tomoya723/FULLMONI-Legacy/FullMoni/FullMoni/iodefine.h

// --------------------------------------------------------------------
// Copylight (C) 2021, Tomoya Sato( https://blog.goo.ne.jp/nacci_tomoya )
//
// This file is part of FullMoni firmwere.
//
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
// filename		:	iodefine.h
// brief		:	FullMoni rev.C IO DEFINE
// author		:	Tomoya Sato
// update		:	2021/02/21
// version		:	1.06
// --------------------------------------------------------------------

// --------------------------------------------------------------------
// 多重インクルード防止
// --------------------------------------------------------------------
#ifndef _IODEFINE_H_
#define _IODEFINE_H_

/************************************************************************/
/*      H8SX/1655 Group Include File                       Version 1.0  */
/************************************************************************/
struct st_usb {                                         /* struct USBF  */
              union {                                   /* IFR0         */
                    unsigned char BYTE;                 /*  Byte Access */
                    struct {                            /*  Bit  Access */
                           unsigned char BRST    :1;    /*    BRST      */
                           unsigned char EP1FULL :1;    /*    EP1FULL   */
                           unsigned char EP2TR   :1;    /*    EP2TR     */
                           unsigned char EP2EMPTY:1;    /*    EP2EMPTY  */
                           unsigned char SETUPTS :1;    /*    SETUPTS   */
                           unsigned char EP0oTS  :1;    /*    EP0oTS    */
                           unsigned char EP0iTR  :1;    /*    EP0iTR    */
                           unsigned char EP0iTS  :1;    /*    EP0iTS    */
                           }      BIT;                  /*              */
                    }           IFR0;                   /*              */
              union {                                   /* IFR1         */
                    unsigned char BYTE;                 /*  Byte Access */
                    struct {                            /*  Bit  Access */
                           unsigned char       :4;      /*              */
                           unsigned char VBUSMN:1;      /*    VBUSMN    */
                           unsigned char EP3TR :1;      /*    EP3TR     */
                           unsigned char EP3TS :1;      /*    EP3TS     */
                           unsigned char VBUSF :1;      /*    VBUSF     */
                           }      BIT;                  /*              */
                    }           IFR1;                   /*              */
              union {                                   /* IFR2         */
                    unsigned char BYTE;                 /*  Byte Access */
                    struct {                            /*  Bit  Access */
                           unsigned char      :2;       /*              */
                           unsigned char SURSS:1;       /*    SURSS     */
                           unsigned char SURSF:1;       /*    SURSF     */
                           unsigned char CFDN :1;       /*    CFDN      */
                           unsigned char      :1;       /*              */
                           unsigned char SETC :1;       /*    SETC      */
                           unsigned char SETI :1;       /*    SETI      */
                           }      BIT;                  /*              */
                    }           IFR2;                   /*              */
              char              wk1;                    /*              */
              union {                                   /* IER0         */
                    unsigned char BYTE;                 /*  Byte Access */
                    struct {                            /*  Bit  Access */
                           unsigned char BRST    :1;    /*    BRST      */
                           unsigned char EP1FULL :1;    /*    EP1FULL   */
                           unsigned char EP2TR   :1;    /*    EP2TR     */
                           unsigned char EP2EMPTY:1;    /*    EP2EMPTY  */
                           unsigned char SETUPTS :1;    /*    SETUPTS   */
                           unsigned char EP0oTS  :1;    /*    EP0oTS    */
                           unsigned char EP0iTR  :1;    /*    EP0iTR    */
                           unsigned char EP0iTS  :1;    /*    EP0iTS    */
                           }      BIT;                  /*              */
                    }           IER0;                   /*              */
              union {                                   /* IER1         */
                    unsigned char BYTE;                 /*  Byte Access */
                    struct {                            /*  Bit  Access */
                           unsigned char       :5;      /*              */
                           unsigned char EP3TR :1;      /*    EP3TR     */
                           unsigned char EP3TS :1;      /*    EP3TS     */
                           unsigned char VBUSF :1;      /*    VBUSF     */
                           }      BIT;                  /*              */
                    }           IER1;                   /*              */
              union {                                   /* IER2         */
                    unsigned char BYTE;                 /*  Byte Access */
                    struct {                            /*  Bit  Access */
                           unsigned char SSRSME:1;      /*    SSRSME    */
                           unsigned char       :2;      /*              */
                           unsigned char SURSE :1;      /*    SURSE     */
                           unsigned char CFDN  :1;      /*    CFDN      */
                           unsigned char       :1;      /*              */
                           unsigned char SETCE :1;      /*    SETCE     */
                           unsigned char SETIE :1;      /*    SETIE     */
                           }      BIT;                  /*              */
                    }           IER2;                   /*              */
              char              wk2;                    /*              */
              union {                                   /* ISR0         */
                    unsigned char BYTE;                 /*  Byte Access */
                    struct {                            /*  Bit  Access */
                           unsigned char BRST    :1;    /*    BRST      */
                           unsigned char EP1FULL :1;    /*    EP1FULL   */
                           unsigned char EP2TR   :1;    /*    EP2TR     */
                           unsigned char EP2EMPTY:1;    /*    EP2EMPTY  */
                           unsigned char SETUPTS :1;    /*    SETUPTS   */
                           unsigned char EP0oTS  :1;    /*    EP0oTS    */
                           unsigned char EP0iTR  :1;    /*    EP0iTR    */
                           unsigned char EP0iTS  :1;    /*    EP0iTS    */
                           }      BIT;                  /*              */
                    }           ISR0;                   /*              */
              union {                                   /* ISR1         */
                    unsigned char BYTE;                 /*  Byte Access */
                    struct {                            /*  Bit  Access */
                           unsigned char       :5;      /*              */
                           unsigned char EP3TR :1;      /*    EP3TR     */
                           unsigned char EP3TS :1;      /*    EP3TS     */
                           unsigned char VBUSF :1;      /*    VBUSF     */
                           }      BIT;                  /*              */
                    }           ISR1;                   /*              */
              union {                                   /* ISR2         */
                    unsigned char BYTE;                 /*  Byte Access */
                    struct {                            /*  Bit  Access */
                           unsigned char      :3;       /*              */
                           unsigned char SURSE:1;       /*    SURSE     */
                           unsigned char CFDN :1;       /*    CFDN      */
                           unsigned char      :1;       /*              */
                           unsigned char SETCE:1;       /*    SETCE     */
                           unsigned char SETIE:1;       /*    SETIE     */
                           }      BIT;                  /*              */
                    }           ISR2;                   /*              */
              char              wk3;                    /*              */
              unsigned char     EPDR0i;                 /* EPDR0i       */
              unsigned char     EPDR0o;                 /* EPDR0o       */
              unsigned char     EPDR0s;                 /* EPDR0s       */
              char              wk4;                    /*              */
              unsigned char     EPDR1;                  /* EPDR1        */
              char              wk5[3];                 /*              */
              unsigned char     EPDR2;                  /* EPDR2        */
              char              wk6[3];                 /*              */
              unsigned char     EPDR3;                  /* EPDR3        */
              char              wk7[11];                /*              */
              unsigned char     EPSZ0o;                 /* EPSZ0o       */
              unsigned char     EPSZ1;                  /* EPSZ1        */
              char              wk8;                    /*              */
              union {                                   /* DASTS        */
                    unsigned char BYTE;                 /*  Byte Access */
                    struct {                            /*  Bit  Access */
                           unsigned char       :2;      /*              */
                           unsigned char EP3DE :1;      /*    EP3DE     */
                           unsigned char EP2DE :1;      /*    EP2DE     */
                           unsigned char       :3;      /*              */
                           unsigned char EP0iDE:1;      /*    EP0iDE    */
                           }      BIT;                  /*              */
                    }           DASTS;                  /*              */
              union {                                   /* FCLR         */
                    unsigned char BYTE;                 /*  Byte Access */
                    struct {                            /*  Bit  Access */
                           unsigned char        :1;     /*              */
                           unsigned char EP3CLR :1;     /*    EP3CLR    */
                           unsigned char EP1CLR :1;     /*    EP1CLR    */
                           unsigned char EP2CLR :1;     /*    EP2CLR    */
                           unsigned char        :2;     /*              */
                           unsigned char EP0oCLR:1;     /*    EP0oCLR   */
                           unsigned char EP0iCLR:1;     /*    EP0iCLR   */
                           }      BIT;                  /*              */
                    }           FCLR;                   /*              */
              char              wk9;                    /*              */
              union {                                   /* EPSTL        */
                    unsigned char BYTE;                 /*  Byte Access */
                    struct {                            /*  Bit  Access */
                           unsigned char       :4;      /*              */
                           unsigned char EP3STL:1;      /*    EP3STL    */
                           unsigned char EP2STL:1;      /*    EP2STL    */
                           unsigned char EP1STL:1;      /*    EP1STL    */
                           unsigned char EP0STL:1;      /*    EP0STL    */
                           }      BIT;                  /*              */
                    }           EPSTL;                  /*              */
              char              wk10;                   /*              */
              union {                                   /* TRG          */
                    unsigned char BYTE;                 /*  Byte Access */
                    struct {                            /*  Bit  Access */
                           unsigned char         :1;    /*              */
                           unsigned char EP3PKTE :1;    /*    EP3PKTE   */
                           unsigned char EP1RDFN :1;    /*    EP1RDFN   */
                           unsigned char EP2PKTE :1;    /*    EP2PKTE   */
                           unsigned char         :1;    /*              */
                           unsigned char EP0sRDFN:1;    /*    EP0sRDFN  */
                           unsigned char EP0oRDFN:1;    /*    EP0oRDFN  */
                           unsigned char EP0iPKTE:1;    /*    EP0iPKTE  */
                           }      BIT;                  /*              */
                    }           TRG;                    /*              */
              union {                                   /* DMA          */
                    unsigned char BYTE;                 /*  Byte Access */
                    struct {                            /*  Bit  Access */
                           unsigned char         :5;    /*              */
                           unsigned char PULLUPE :1;    /*    PULLUP_E  */
                           unsigned char EP2DMAE :1;    /*    EP2DMAE   */
                           unsigned char EP1DMAE :1;    /*    EP1DMAE   */
                           }      BIT;                  /*              */
                    }           DMA;                    /*              */
              union {                                   /* CVR          */
                    unsigned char BYTE;                 /*  Byte Access */
                    struct {                            /*  Bit  Access */
                           unsigned char CNFV:2;        /*    CNFV      */
                           unsigned char INTV:2;        /*    INTV      */
                           unsigned char     :1;        /*              */
                           unsigned char ALTV:3;        /*    ALTV      */
                           }      BIT;                  /*              */
                    }           CVR;                    /*              */
              union {                                   /* CTLR         */
                    unsigned char BYTE;                 /*  Byte Access */
                    struct {                            /*  Bit  Access */
                           unsigned char      :3;       /*              */
                           unsigned char RWUPS:1;       /*    RWUPS     */
                           unsigned char RSME :1;       /*    RSME      */
                           unsigned char PWMD :1;       /*    PWMD      */
                           unsigned char ASCE :1;       /*    ASCE      */
                           }      BIT;                  /*              */
                    }           CTLR;                   /*              */
              char              wk11[2];                /*              */
              unsigned char     EPIR;                   /* EPIR         */
              char              wk12[17];               /*              */
              union {                                   /* TRNTREG0     */
                    unsigned char BYTE;                 /*  Byte Access */
                    struct {                            /*  Bit  Access */
                           unsigned char PTSTE  :1;     /*    PTSTE     */
                           unsigned char        :3;     /*              */
                           unsigned char SUSPEND:1;     /*    SUSPEND   */
                           unsigned char txenl  :1;     /*    txenl     */
                           unsigned char Txse0  :1;     /*    Txse0     */
                           unsigned char Txdata :1;     /*    Txdata    */
                           }      BIT;                  /*              */
                    }           TRNTREG0;               /*              */
              union {                                   /* TRNTREG1     */
                    unsigned char BYTE;                 /*  Byte Access */
                    struct {                            /*  Bit  Access */
                           unsigned char          :5;   /*              */
                           unsigned char xverdata :1;   /*    xver_data */
                           unsigned char dpls     :1;   /*    dpls      */
                           unsigned char dmns     :1;   /*    dmns      */
                           }      BIT;                  /*              */
                     }          TRNTREG1;               /*              */
};                                                      /*              */
struct st_p1 {                                          /* struct P1    */
             unsigned char      DDR;                    /* P1DDR        */
             char               wk1[15];                /*              */
             union {                                    /* P1ICR        */
                   unsigned char BYTE;                  /*  Byte Access */
                   struct {                             /*  Bit  Access */
                          unsigned char B7:1;           /*    Bit 7     */
                          unsigned char B6:1;           /*    Bit 6     */
                          unsigned char B5:1;           /*    Bit 5     */
                          unsigned char B4:1;           /*    Bit 4     */
                          unsigned char B3:1;           /*    Bit 3     */
                          unsigned char B2:1;           /*    Bit 2     */
                          unsigned char B1:1;           /*    Bit 1     */
                          unsigned char B0:1;           /*    Bit 0     */
                          }      BIT;                   /*              */
                   }            ICR;                    /*              */
             char               wk2[943];               /*              */
             union {                                    /* P1PORT       */
                   unsigned char BYTE;                  /*  Byte Access */
                   struct {                             /*  Bit  Access */
                          unsigned char B7:1;           /*    Bit 7     */
                          unsigned char B6:1;           /*    Bit 6     */
                          unsigned char B5:1;           /*    Bit 5     */
                          unsigned char B4:1;           /*    Bit 4     */
                          unsigned char B3:1;           /*    Bit 3     */
                          unsigned char B2:1;           /*    Bit 2     */
                          unsigned char B1:1;           /*    Bit 1     */
                          unsigned char B0:1;           /*    Bit 0     */
                          }      BIT;                   /*              */
                   }            PORT;                   /*              */
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
                    struct {                            /*  Bit  Access */
                           unsigned char CS7S:2;        /*    CS7S      */
                           unsigned char CS6S:2;        /*    CS6S      */
                           unsigned char CS5S:2;        /*    CS5S      */
                           }      BIT;                  /*              */
                    }           PFCR1;                  /*              */
              union {                                   /* PFCR2        */
                    unsigned char BYTE;                 /*  Byte Access */
                    struct {                            /*  Bit  Access */
                           unsigned char      :1;       /*              */
                           unsigned char CS2S :1;       /*    CS2S      */
                           unsigned char BSS  :1;       /*    BSS       */
                           unsigned char BSE  :1;       /*    BSE       */
                           unsigned char      :1;       /*              */
                           unsigned char RDWRE:1;       /*    RDWRE     */
                           unsigned char ASOE :1;       /*    ASOE      */
                           unsigned char      :1;       /*              */
                           }      BIT;                  /*              */
                    }           PFCR2;                  /*              */
              char              wk1;                    /*              */
              union {                                   /* PFCR4        */
                    unsigned char BYTE;                 /*  Byte Access */
                    struct {                            /*  Bit  Access */
                           unsigned char     :3;        /*              */
                           unsigned char A20E:1;        /*    A20E      */
                           unsigned char A19E:1;        /*    A19E      */
                           unsigned char A18E:1;        /*    A18E      */
                           unsigned char A17E:1;        /*    A17E      */
                           unsigned char A16E:1;        /*    A16E      */
                           }      BIT;                  /*              */
                    }           PFCR4;                  /*              */
              char              wk2;                    /*              */
              union {                                   /* PFCR6        */
                    unsigned char BYTE;                 /*  Byte Access */
                    struct {                            /*  Bit  Access */
                           unsigned char       :1;      /*              */
                           unsigned char LHWROE:1;      /*    LHWROE    */
                           unsigned char       :2;      /*              */
                           unsigned char TCLKS :1;      /*    TCLKS     */
                           }      BIT;                  /*              */
                    }           PFCR6;                  /*              */
              union {                                   /* PFCR7        */
                    unsigned char BYTE;                 /*  Byte Access */
                    struct {                            /*  Bit  Access */
                           unsigned char DMAS3:2;       /*    DMAS3     */
                           unsigned char DMAS2:2;       /*    DMAS2     */
                           unsigned char DMAS1:2;       /*    DMAS1     */
                           unsigned char DMAS0:2;       /*    DMAS0     */
                           }      BIT;                  /*              */
                    }           PFCR7;                  /*              */
              union {                                   /* PFCR8        */
                    unsigned char BYTE;                 /*  Byte Access */
                    struct {                            /*  Bit  Access */
                           unsigned char        :4;     /*              */
                           unsigned char EDMAS1A:1;     /*    EDMAS1A   */
                           unsigned char EDMAS1B:1;     /*    EDMAS1B   */
                           unsigned char EDMAS0A:1;     /*    EDMAS0A   */
                           unsigned char EDMAS0B:1;     /*    EDMAS0B   */
                           }      BIT;                  /*              */
                    }           PFCR8;                  /*              */
              union {                                   /* PFCR9        */
                    unsigned char BYTE;                 /*  Byte Access */
                    struct {                            /*  Bit  Access */
                           unsigned char TPUMS5 :1;     /*    TPUMS5    */
                           unsigned char TPUMS4 :1;     /*    TPUMS4    */
                           unsigned char TPUMS3A:1;     /*    TPUMS3A   */
                           unsigned char TPUMS3B:1;     /*    TPUMS3B   */
                           }      BIT;                  /*              */
                    }           PFCR9;                  /*              */
              union {                                   /* PFCRA        */
                    unsigned char BYTE;                 /*  Byte Access */
                    struct {                            /*  Bit  Access */
                           unsigned char TPUMS11:1;     /*    TPUMS11   */
                           unsigned char TPUMS10:1;     /*    TPUMS10   */
                           unsigned char TPUMS9A:1;     /*    TPUMS9A   */
                           unsigned char TPUMS9B:1;     /*    TPUMS9B   */
                           unsigned char TPUMS8 :1;     /*    TPUMS8    */
                           unsigned char TPUMS7 :1;     /*    TPUMS7    */
                           unsigned char TPUMS6A:1;     /*    TPUMS6A   */
                           unsigned char TPUMS6B:1;     /*    TPUMS6B   */
                           }      BIT;                  /*              */
                    }           PFCRA;                  /*              */
              union {                                   /* PFCRB        */
                    unsigned char BYTE;                 /*  Byte Access */
                    struct {                            /*  Bit  Access */
                           unsigned char      :4;       /*              */
                           unsigned char ITS11:1;       /*    ITS11     */
                           unsigned char ITS10:1;       /*    ITS10     */
                           unsigned char ITS9 :1;       /*    ITS9      */
                           unsigned char ITS8 :1;       /*    ITS8      */
                           }      BIT;                  /*              */
                    }           PFCRB;                  /*              */
              union {                                   /* PFCRC        */
                    unsigned char BYTE;                 /*  Byte Access */
                    struct {                            /*  Bit  Access */
                           unsigned char ITS7:1;        /*    ITS7      */
                           unsigned char ITS6:1;        /*    ITS6      */
                           unsigned char ITS5:1;        /*    ITS5      */
                           unsigned char ITS4:1;        /*    ITS4      */
                           unsigned char ITS3:1;        /*    ITS3      */
                           unsigned char ITS2:1;        /*    ITS2      */
                           unsigned char ITS1:1;        /*    ITS1      */
                           unsigned char ITS0:1;        /*    ITS0      */
                           }      BIT;                  /*              */
                    }           PFCRC;                  /*              */
              union {                                   /* PFCRD        */
                    unsigned char BYTE;                 /*  Byte Access */
                    struct {                            /*  Bit  Access */
                           unsigned char PCJKE:1;       /*    PCJKE     */
                           }      BIT;                  /*              */
                    }           PFCRD;                  /*              */
};                                                      /*              */
struct st_intc {                                        /* struct INTC  */
               union {                                  /* SSIER        */
                     unsigned short WORD;               /*  Word Access */
                     struct {                           /*  Bit  Access */
                            unsigned char      :4;      /*              */
                            unsigned char SSI11:1;      /*    SSI11     */
                            unsigned char SSI10:1;      /*    SSI10     */
                            unsigned char SSI9 :1;      /*    SSI9      */
                            unsigned char SSI8 :1;      /*    SSI8      */
                            unsigned char SSI7 :1;      /*    SSI7      */
                            unsigned char SSI6 :1;      /*    SSI6      */
                            unsigned char SSI5 :1;      /*    SSI5      */
                            unsigned char SSI4 :1;      /*    SSI4      */
                            unsigned char SSI3 :1;      /*    SSI3      */
                            unsigned char SSI2 :1;      /*    SSI2      */
                            unsigned char SSI1 :1;      /*    SSI1      */
                            unsigned char SSI0 :1;      /*    SSI0      */
                            }     BIT;                  /*              */
                     }          SSIER;                  /*              */
               char             wk1[368];               /*              */
               union {                                  /* IPRA         */
                     unsigned short WORD;               /*  Word Access */
                     struct {                           /*  Bit  Access */
                            unsigned char      :1;      /*              */
                            unsigned char _IRQ0:3;      /*    IRQ0      */
                            unsigned char      :1;      /*              */
                            unsigned char _IRQ1:3;      /*    IRQ1      */
                            unsigned char      :1;      /*              */
                            unsigned char _IRQ2:3;      /*    IRQ2      */
                            unsigned char      :1;      /*              */
                            unsigned char _IRQ3:3;      /*    IRQ3      */
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
                     unsigned short WORD;               /*  Word Access */
                     struct {                           /*  Bit  Access */
                            unsigned char       :1;     /*              */
                            unsigned char _TPU6V:3;     /*    TCI6V     */
                            unsigned char       :1;     /*              */
                            unsigned char _TPU7A:3;     /*    TGI7AB    */
                            unsigned char       :1;     /*              */
                            unsigned char _TPU7V:3;     /*    TCI7VU    */
                            unsigned char       :1;     /*              */
                            unsigned char _TPU8A:3;     /*    TGI7AB    */
                            }     BIT;                  /*              */
                     }          IPRM;                   /*              */
               union {                                  /* IPRN         */
                     unsigned short WORD;               /*  Word Access */
                     struct {                           /*  Bit  Access */
                            unsigned char        :1;    /*              */
                            unsigned char _TPU8V :3;    /*    TCI8VU    */
                            unsigned char        :1;    /*              */
                            unsigned char _TPU9A :3;    /*    TGI9ABCD  */
                            unsigned char        :1;    /*              */
                            unsigned char _TPU9V :3;    /*    TCI9V     */
                            unsigned char        :1;    /*              */
                            unsigned char _TPU10A:3;    /*    TGI10AB   */
                            }     BIT;                  /*              */
                     }          IPRN;                   /*              */
               union {                                  /* IPRO         */
                     unsigned short WORD;               /*  Word Access */
                     struct {                           /*  Bit  Access */
                            unsigned char        :1;    /*              */
                            unsigned char _TPU10V:3;    /*    TCI10VU   */
                            unsigned char        :1;    /*              */
                            unsigned char _TPU11A:3;    /*    TGI11AB   */
                            unsigned char        :1;    /*              */
                            unsigned char _TPU11V:3;    /*    TCI11VU   */
                            }     BIT;                  /*              */
                     }          IPRO;                   /*              */
               char             wk4[2];                 /*              */
               union {                                  /* IPRQ         */
                     unsigned short WORD;               /*  Word Access */
                     struct {                           /*  Bit  Access */
                            unsigned char      :8;      /*              */
                            unsigned char      :1;      /*              */
                            unsigned char _IIC2:3;      /*    IIC2      */
                            unsigned char      :1;      /*              */
                            unsigned char _SCI5:3;      /*    SCI5      */
                            }     BIT;                  /*              */
                     }          IPRQ;                   /*              */
               union {                                  /* IPRR         */
                     unsigned short WORD;               /*  Word Access */
                     struct {                           /*  Bit  Access */
                            unsigned char       :1;     /*              */
                            unsigned char _SCI6 :3;     /*    SCI6      */
                            unsigned char       :1;     /*              */
                            unsigned char _TMR47:3;     /*    TMR4-7    */
                            unsigned char       :1;     /*              */
                            unsigned char _USB  :3;     /*    USB       */							
                            unsigned char       :1;     /*              */
                            unsigned char _AD1  :3;     /*    AD1       */
                            }     BIT;                  /*              */
                     }          IPRR;                   /*              */
               char             wk5[4];                 /*              */
#if 1               
               union {                                  /* ISCR_H       */
                     unsigned short WORD;               /*  Word Access */
                     struct {                           /*  Bit  Access */
							unsigned char        :8;    /*              */
                            unsigned char IRQ11SC:2;    /*    IRQ11SC   */
                            unsigned char IRQ10SC:2;    /*    IRQ10SC   */
                            unsigned char IRQ9SC :2;    /*    IRQ9SC    */
                            unsigned char IRQ8SC :2;    /*    IRQ8SC    */
                            }      BIT;                 /*              */
                     }          ISCR_H;                 /*              */
               union {                                  /* ISCR_L       */
                     unsigned short WORD;               /*  Word Access */
                     struct {                           /*  Bit  Access */
                            unsigned char IRQ7SC :2;    /*    IRQ7SC    */
                            unsigned char IRQ6SC :2;    /*    IRQ6SC    */
                            unsigned char IRQ5SC :2;    /*    IRQ5SC    */
                            unsigned char IRQ4SC :2;    /*    IRQ4SC    */
                            unsigned char IRQ3SC :2;    /*    IRQ3SC    */
                            unsigned char IRQ2SC :2;    /*    IRQ2SC    */
                            unsigned char IRQ1SC :2;    /*    IRQ1SC    */
                            unsigned char IRQ0SC :2;    /*    IRQ0SC    */
                            }      BIT;                 /*              */
                     }          ISCR_L;                 /*              */
#endif               
#if 0               
               union {                                  /* ISCR         */
                     unsigned long LONG;                /*  Long Access */
                     struct {                           /*  Word Access */
                            unsigned short H;           /*    ISCRH     */
                            unsigned short L;           /*    ISCRL     */
                            }      WORD;                /*              */
                     struct {                           /*  Bit  Access */
							unsigned char        :8;    /*              */
                            unsigned char IRQ11SC:2;    /*    IRQ11SC   */
                            unsigned char IRQ10SC:2;    /*    IRQ10SC   */
                            unsigned char IRQ9SC :2;    /*    IRQ9SC    */
                            unsigned char IRQ8SC :2;    /*    IRQ8SC    */
                            unsigned char IRQ7SC :2;    /*    IRQ7SC    */
                            unsigned char IRQ6SC :2;    /*    IRQ6SC    */
                            unsigned char IRQ5SC :2;    /*    IRQ5SC    */
                            unsigned char IRQ4SC :2;    /*    IRQ4SC    */
                            unsigned char IRQ3SC :2;    /*    IRQ3SC    */
                            unsigned char IRQ2SC :2;    /*    IRQ2SC    */
                            unsigned char IRQ1SC :2;    /*    IRQ1SC    */
                            unsigned char IRQ0SC :2;    /*    IRQ0SC    */
                            }      BIT;                 /*              */
                     }          ISCR;                   /*              */
#endif                     
               char             wk6[454];               /*              */
               union {                                  /* INTCR        */
                     unsigned char BYTE;                /*  Byte Access */
                     struct {                           /*  Bit  Access */
                            unsigned char      :2;      /*              */
                            unsigned char INTM :2;      /*    INTM      */
                            unsigned char NMIEG:1;      /*    NMIEG     */
                            unsigned char      :3;      /*              */
                            }      BIT;                 /*              */
                     }          INTCR;                  /*              */
               union {                                  /* CPUPCR       */
                     unsigned char BYTE;                /*  Byte Access */
                     struct {                           /*  Bit  Access */
                            unsigned char CPUPCE:1;     /*    CPUPCE    */
                            unsigned char DTCP  :3;     /*    DTCP      */
                            unsigned char IPSETE:1;     /*    IPSETE    */
                            unsigned char CPUP  :3;     /*    CPUP      */
                            }      BIT;                 /*              */
                     }          CPUPCR;                 /*              */
               union {                                  /* IER          */
                     unsigned short WORD;               /*  Word Access */
                     struct {                           /*  Bit  Access */
                            unsigned char       :4;     /*              */
                            unsigned char IRQ11E:1;     /*    IRQ11E    */
                            unsigned char IRQ10E:1;     /*    IRQ10E    */
                            unsigned char IRQ9E :1;     /*    IRQ9E     */
                            unsigned char IRQ8E :1;     /*    IRQ8E     */
                            unsigned char IRQ7E :1;     /*    IRQ7E     */
                            unsigned char IRQ6E :1;     /*    IRQ6E     */
                            unsigned char IRQ5E :1;     /*    IRQ5E     */
                            unsigned char IRQ4E :1;     /*    IRQ4E     */
                            unsigned char IRQ3E :1;     /*    IRQ3E     */
                            unsigned char IRQ2E :1;     /*    IRQ2E     */
                            unsigned char IRQ1E :1;     /*    IRQ1E     */
                            unsigned char IRQ0E :1;     /*    IRQ0E     */
                            }     BIT;                  /*              */
                     }          IER;                    /*              */
               union {                                  /* ISR          */
                     unsigned short WORD;               /*  Word Access */
                     struct {                           /*  Bit  Access */
                            unsigned char       :4;     /*              */
                            unsigned char IRQ11F:1;     /*    IRQ11F    */
                            unsigned char IRQ10F:1;     /*    IRQ10F    */
                            unsigned char IRQ9F :1;     /*    IRQ9F     */
                            unsigned char IRQ8F :1;     /*    IRQ8F     */
                            unsigned char IRQ7F :1;     /*    IRQ7F     */
                            unsigned char IRQ6F :1;     /*    IRQ6F     */
                            unsigned char IRQ5F :1;     /*    IRQ5F     */
                            unsigned char IRQ4F :1;     /*    IRQ4F     */
                            unsigned char IRQ3F :1;     /*    IRQ3F     */
                            unsigned char IRQ2F :1;     /*    IRQ2F     */
                            unsigned char IRQ1F :1;     /*    IRQ1F     */
                            unsigned char IRQ0F :1;     /*    IRQ0F     */
                            }     BIT;                  /*              */
                     }          ISR;                    /*              */
};                                                      /*              */
struct st_dmac0 {                                       /* struct DMAC0 */
                void           *DSAR;                   /* DSAR         */
                void           *DDAR;                   /* DDAR         */
                unsigned long   DOFR;                   /* DOFR         */
                unsigned long   DTCR;                   /* DTCR         */
                unsigned long   DBSR;                   /* DBSR         */
                union {                                 /* DMDR         */
                      unsigned long LONG;               /*  Long Access */
                      struct {                          /*  Bit  Access */
                             unsigned char DTE  :1;     /*    DTE       */
                             unsigned char DACKE:1;     /*    DACKE     */
                             unsigned char TENDE:1;     /*    TENDE     */
                             unsigned char      :1;     /*              */
                             unsigned char DREQS:1;     /*    DREQS     */
                             unsigned char NRD  :1;     /*    NRD       */
                             unsigned char      :2;     /*              */
                             unsigned char ACT  :1;     /*    ACT       */
                             unsigned char      :3;     /*              */
                             unsigned char ERRF :1;     /*    ERRF      */
                             unsigned char      :1;     /*              */
                             unsigned char ESIF :1;     /*    ESIF      */
                             unsigned char DTIF :1;     /*    DTIF      */
                             unsigned char DTSZ :2;     /*    DTSZ      */
                             unsigned char MDS  :2;     /*    MDS       */
                             unsigned char TSEIE:1;     /*    TSEIE     */
                             unsigned char      :1;     /*              */
                             unsigned char ESIE :1;     /*    ESIE      */
                             unsigned char DTIE :1;     /*    DTIE      */
                             unsigned char DTF  :2;     /*    DTF       */
                             unsigned char DTA  :1;     /*    DTA       */
                             unsigned char      :2;     /*              */
                             unsigned char DMAP :3;     /*    DMAP      */
                             }      BIT;                /*              */
                      }         DMDR;                   /*              */
                union {                                 /* DACR         */
                      unsigned long LONG;               /*  Long Access */
                      struct {                          /*  Bit  Access */
                             unsigned char AMS  :1;     /*    AMS       */
                             unsigned char DIRS :1;     /*    DIRS      */
                             unsigned char      :3;     /*              */
                             unsigned char RPTIE:1;     /*    RPTIE     */
                             unsigned char ARS  :2;     /*    ARS       */
                             unsigned char      :2;     /*              */
                             unsigned char SAT  :2;     /*    SAT       */
                             unsigned char      :2;     /*              */
                             unsigned char DAT  :2;     /*    DAT       */
                             unsigned char SARIE:1;     /*    SARIE     */
                             unsigned char      :2;     /*              */
                             unsigned char SARA :5;     /*    SARA      */
                             unsigned char DARIE:1;     /*    DARIE     */
                             unsigned char      :2;     /*              */
                             unsigned char DARA :5;     /*    DARA      */
                             }      BIT;                /*              */
                      }         DACR;                   /*              */
                char            wk[260];                /*              */
                unsigned char   DMRSR;                  /* DMRSR        */
};                                                      /*              */
struct st_dmac1 {                                       /* struct DMAC1 */
                void           *DSAR;                   /* DSAR         */
                void           *DDAR;                   /* DDAR         */
                unsigned long   DOFR;                   /* DOFR         */
                unsigned long   DTCR;                   /* DTCR         */
                unsigned long   DBSR;                   /* DBSR         */
                union {                                 /* DMDR         */
                      unsigned long LONG;               /*  Long Access */
                      struct {                          /*  Bit  Access */
                             unsigned char DTE  :1;     /*    DTE       */
                             unsigned char DACKE:1;     /*    DACKE     */
                             unsigned char TENDE:1;     /*    TENDE     */
                             unsigned char      :1;     /*              */
                             unsigned char DREQS:1;     /*    DREQS     */
                             unsigned char NRD  :1;     /*    NRD       */
                             unsigned char      :2;     /*              */
                             unsigned char ACT  :1;     /*    ACT       */
                             unsigned char      :5;     /*              */
                             unsigned char ESIF :1;     /*    ESIF      */
                             unsigned char DTIF :1;     /*    DTIF      */
                             unsigned char DTSZ :2;     /*    DTSZ      */
                             unsigned char MDS  :2;     /*    MDS       */
                             unsigned char TSEIE:1;     /*    TSEIE     */
                             unsigned char      :1;     /*              */
                             unsigned char ESIE :1;     /*    ESIE      */
                             unsigned char DTIE :1;     /*    DTIE      */
                             unsigned char DTF  :2;     /*    DTF       */
                             unsigned char DTA  :1;     /*    DTA       */
                             unsigned char      :2;     /*              */
                             unsigned char DMAP :3;     /*    DMAP      */
                             }      BIT;                /*              */
                      }         DMDR;                   /*              */
                union {                                 /* DACR         */
                      unsigned long LONG;               /*  Long Access */
                      struct {                          /*  Bit  Access */
                             unsigned char AMS  :1;     /*    AMS       */
                             unsigned char DIRS :1;     /*    DIRS      */
                             unsigned char      :3;     /*              */
                             unsigned char RPTIE:1;     /*    RPTIE     */
                             unsigned char ARS  :2;     /*    ARS       */
                             unsigned char      :2;     /*              */
                             unsigned char SAT  :2;     /*    SAT       */
                             unsigned char      :2;     /*              */
                             unsigned char DAT  :2;     /*    DAT       */
                             unsigned char SARIE:1;     /*    SARIE     */
                             unsigned char      :2;     /*              */
                             unsigned char SARA :5;     /*    SARA      */
                             unsigned char DARIE:1;     /*    DARIE     */
                             unsigned char      :2;     /*              */
                             unsigned char DARA :5;     /*    DARA      */
                             }      BIT;                /*              */
                      }         DACR;                   /*              */
                char            wk[229];                /*              */
                unsigned char   DMRSR;                  /* DMRSR        */
};                                                      /*              */
struct st_dmac2 {                                       /* struct DMAC2 */
                void           *DSAR;                   /* DSAR         */
                void           *DDAR;                   /* DDAR         */
                unsigned long   DOFR;                   /* DOFR         */
                unsigned long   DTCR;                   /* DTCR         */
                unsigned long   DBSR;                   /* DBSR         */
                union {                                 /* DMDR         */
                      unsigned long LONG;               /*  Long Access */
                      struct {                          /*  Bit  Access */
                             unsigned char DTE  :1;     /*    DTE       */
                             unsigned char DACKE:1;     /*    DACKE     */
                             unsigned char TENDE:1;     /*    TENDE     */
                             unsigned char      :1;     /*              */
                             unsigned char DREQS:1;     /*    DREQS     */
                             unsigned char NRD  :1;     /*    NRD       */
                             unsigned char      :2;     /*              */
                             unsigned char ACT  :1;     /*    ACT       */
                             unsigned char      :5;     /*              */
                             unsigned char ESIF :1;     /*    ESIF      */
                             unsigned char DTIF :1;     /*    DTIF      */
                             unsigned char DTSZ :2;     /*    DTSZ      */
                             unsigned char MDS  :2;     /*    MDS       */
                             unsigned char TSEIE:1;     /*    TSEIE     */
                             unsigned char      :1;     /*              */
                             unsigned char ESIE :1;     /*    ESIE      */
                             unsigned char DTIE :1;     /*    DTIE      */
                             unsigned char DTF  :2;     /*    DTF       */
                             unsigned char DTA  :1;     /*    DTA       */
                             unsigned char      :2;     /*              */
                             unsigned char DMAP :3;     /*    DMAP      */
                             }      BIT;                /*              */
                      }         DMDR;                   /*              */
                union {                                 /* DACR         */
                      unsigned long LONG;               /*  Long Access */
                      struct {                          /*  Bit  Access */
                             unsigned char AMS  :1;     /*    AMS       */
                             unsigned char DIRS :1;     /*    DIRS      */
                             unsigned char      :3;     /*              */
                             unsigned char RPTIE:1;     /*    RPTIE     */
                             unsigned char ARS  :2;     /*    ARS       */
                             unsigned char      :2;     /*              */
                             unsigned char SAT  :2;     /*    SAT       */
                             unsigned char      :2;     /*              */
                             unsigned char DAT  :2;     /*    DAT       */
                             unsigned char SARIE:1;     /*    SARIE     */
                             unsigned char      :2;     /*              */
                             unsigned char SARA :5;     /*    SARA      */
                             unsigned char DARIE:1;     /*    DARIE     */
                             unsigned char      :2;     /*              */
                             unsigned char DARA :5;     /*    DARA      */
                             }      BIT;                /*              */
                      }         DACR;                   /*              */
                char            wk[198];                /*              */
                unsigned char   DMRSR;                  /* DMRSR        */
};                                                      /*              */
struct st_dmac3 {                                       /* struct DMAC3 */
                void           *DSAR;                   /* DSAR         */
                void           *DDAR;                   /* DDAR         */
                unsigned long   DOFR;                   /* DOFR         */
                unsigned long   DTCR;                   /* DTCR         */
                unsigned long   DBSR;                   /* DBSR         */
                union {                                 /* DMDR         */
                      unsigned long LONG;               /*  Long Access */
                      struct {                          /*  Bit  Access */
                             unsigned char DTE  :1;     /*    DTE       */
                             unsigned char DACKE:1;     /*    DACKE     */
                             unsigned char TENDE:1;     /*    TENDE     */
                             unsigned char      :1;     /*              */
                             unsigned char DREQS:1;     /*    DREQS     */
                             unsigned char NRD  :1;     /*    NRD       */
                             unsigned char      :2;     /*              */
                             unsigned char ACT  :1;     /*    ACT       */
                             unsigned char      :5;     /*              */
                             unsigned char ESIF :1;     /*    ESIF      */
                             unsigned char DTIF :1;     /*    DTIF      */
                             unsigned char DTSZ :2;     /*    DTSZ      */
                             unsigned char MDS  :2;     /*    MDS       */
                             unsigned char TSEIE:1;     /*    TSEIE     */
                             unsigned char      :1;     /*              */
                             unsigned char ESIE :1;     /*    ESIE      */
                             unsigned char DTIE :1;     /*    DTIE      */
                             unsigned char DTF  :2;     /*    DTF       */
                             unsigned char DTA  :1;     /*    DTA       */
                             unsigned char      :2;     /*              */
                             unsigned char DMAP :3;     /*    DMAP      */
                             }      BIT;                /*              */
                      }         DMDR;                   /*              */
                union {                                 /* DACR         */
                      unsigned long LONG;               /*  Long Access */
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
